eastonja/SIM-69/SIM-69 MainBoard v1.0/SIM-69-IIC-OLED.jpg

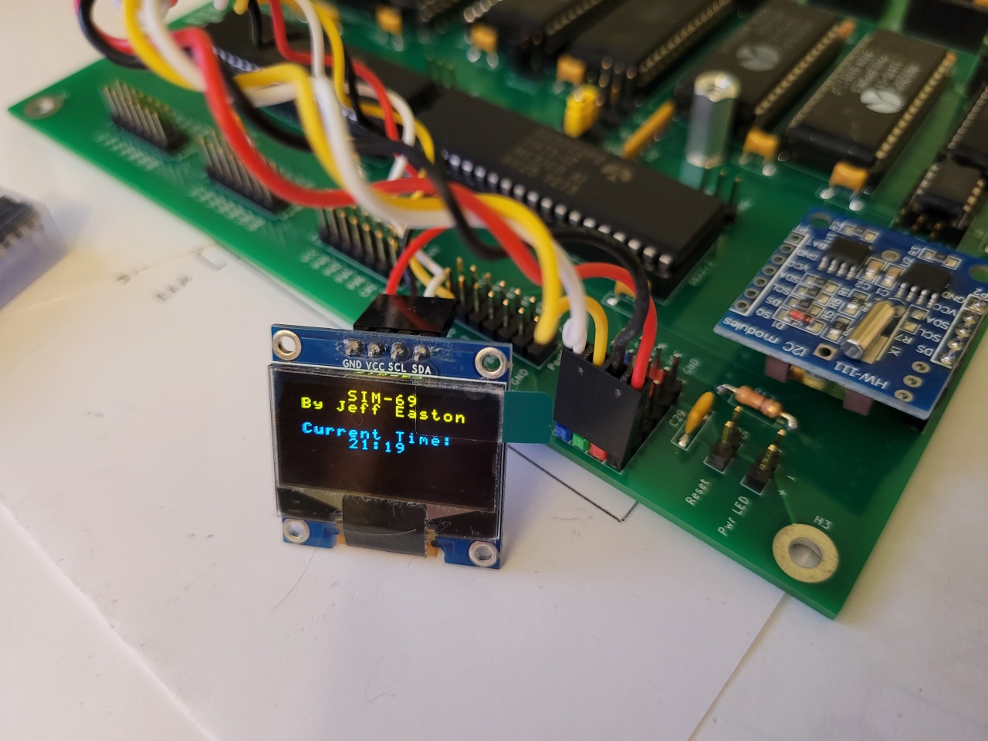
SIM-69 MainBoard v1.0/SIM-69-IIC-OLED.jpg
